pestalella/FontDelGat/Firmware/MainBoard/OutputControl.cpp

#include "OutputControl.h"

// OutputControl::OutputControl(HardwareSerial &mySerial) :
//     // dacChannelA(),
//     // dacChannelB()
// {

// }
// void OutputControl::begin()
// {
//     // dacChannelA.begin();
//     // dacChannelB.begin();
// }

// int OutputControl::setOutput(Channel chSel, int voltagex1000)
// {

// }

// private:
//     // MCP4725 dacChannelA;
//     // MCP4725 dacChannelB;
//     HardwareSerial &mySerial;
// };
